jaka87/vetercek_WS/3D prints/WS box/PG gland insert 3.stl

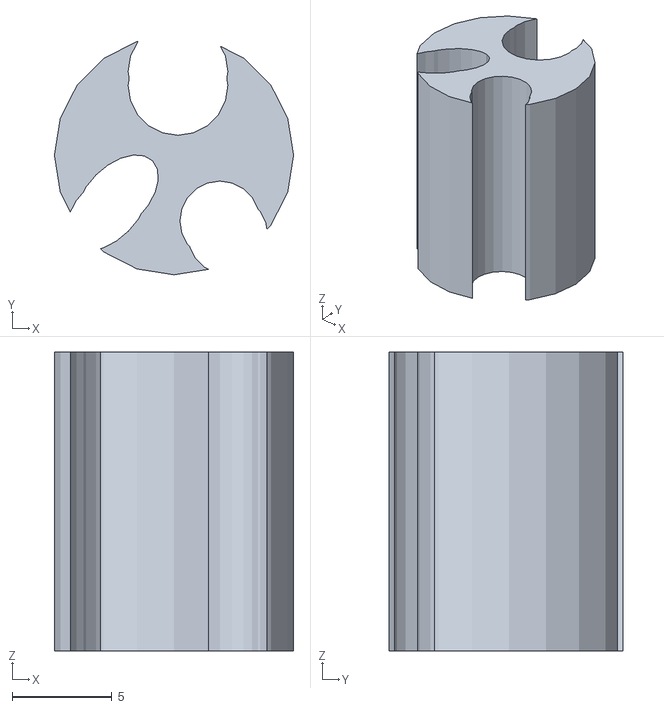
[picture p18: CAD file, 2021-04-03]
3D prints/WS box/PG gland insert 3.stl
12.0 x 11.7 x 15.0
