jaka87/vetercek_WS/3D prints/solar/solar glued.stl

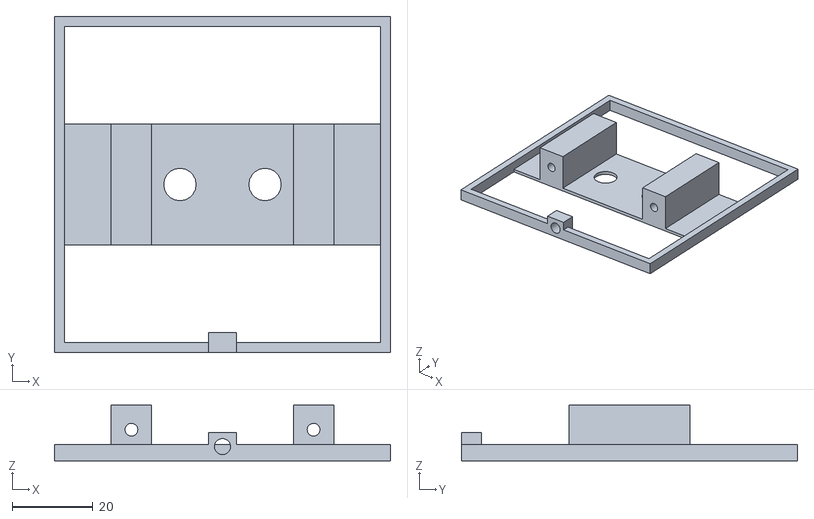
[picture p19: CAD file, 2021-07-03, an earlier design]
3D prints/solar/solar glued.stl
83.0 x 83.0 x 13.7
