jaka87/vetercek_WS/vetercek_SIM7070_modbus/src/BME/Zanshin_BME680.h

// clang-format off
/*! @file Zanshin_BME680.h

@mainpage Arduino Library to access and control a Bosch BME680 Environmental Sensor

@section Zanshin_BME680_section Description

Class definition header for the Bosch BME680 temperature / humidity / pressure / air quality sensor.
The device is described at https://www.bosch-sensortec.com/bst/products/all_products/BME680 and the
datasheet is available from Bosch at
https://ae-bst.resource.bosch.com/media/_tech/media/datasheets/BST-BME680-DS001-00.pdf
\n\n

The BME680 can use either SPI or I2C for communications. This library supports I2C at various bus
speeds as well as SPI using either the standard Arduino hardware SPI or software SPI. Depending upon
the pin configuration a BME680 can have 2 distinct I2C addresses - either 0x76 or 0x77.\n\n

The most recent version of the library is available at https://github.com/SV-Zanshin/BME680 and
extensive documentation of the library as well as descriptions of the various example programs are
described in the project's wiki pages located at https://github.com/SV-Zanshin/BME680/wiki
\n
The BME680 is an extremely small physical package that is so tiny as to be impossible to solder at
home, hence it will be used as part of a third-party breakout board. There are several such boards
available at this time, for example:\n

Company  | Link
-------  | ----------
SparkFun | https://www.sparkfun.com/products/14570
BlueDot  | https://www.bluedot.space/sensor-boards/bme680/
Adafruit |
https://learn.adafruit.com/adafruit-BME680-humidity-barometric-pressure-temperature-sensor-breakout

\n
Bosch supplies sample software that runs on various platforms, including the Arduino family; this
can be downloaded at https://github.com/BoschSensortec/BSEC-Arduino-library. This software is part
of the Bosch "BSEC" (Bosch Sensortec Environmental Cluster) framework and is somewhat bulky and
rather unwieldy for typical Arduino applications, it won't run on most Arduinos and the only example
is for the Arduino Mega 2560 (due to the memory required), hence the decision to make this compact
and rather less abstract library that will run on typical Arduino hardware.

@section license License

This program is free software: you can redistribute it and/or modify it under the terms of the GNU
General Public License as published by the Free Software Foundation, either version 3 of the
License, or (at your option) any later version. This program is distributed in the hope that it will
be useful, but WITHOUT ANY WARRANTY; without even the implied warranty of MERCHANTABILITY or FITNESS
FOR A PARTICULAR PURPOSE.  See the GNU General Public License for more details. You should have
received a copy of the GNU General Public License along with this program.  If not, see
<http://www.gnu.org/licenses/>.

@section author Author

Written by Arnd, https://github.com/SV-Zanshin

@section versions Changelog

Version | Date       | Developer  | Comments
------- | ---------- | ---------- | ---------------------------------------------------------------
1.0.10  | 2020-12-03 | SV-Zanshin | Issue #34 Enhancements from Alain2019 - added measurement functionality
1.0.10  | 2020-12-02 | SV-Zanshin | Issue #33 Optimize library code for size, performance, initializers
1.0.10  | 2020-10-19 | Alain2019  | Issue #32 Change division to bit shifts for clarity
1.0.10  | 2020-10-10 | Alain2019  | Issue #31 Incorrect computation of _H1 and _H2
1.0.9   | 2020-09-27 | SV-Zanshin | Issue #26 added return status for getSensorData
1.0.9   | 2020-09-27 | SV-Zanshin | Issue #26 Corrected computation of gas heater resistance value
1.0.9   | 2020-06-28 | SV-Zanshin | Issue #25 Reformat according to standard c++ style
1.0.8   | 2020-06-20 | SV-Zanshin | Issue #22 added "getI2CAddress()" function
1.0.6   | 2020-05-25 | SV-Zanshin | Issue #17 return value for "setOversampling()"
1.0.6   | 2020-05-25 | SV-Zanshin | Issue #16 I2C "reset()" when using 2 devices
1.0.6   | 2020-05-25 | SV-Zanshin |           General formatting of comments and spell-checking
1.0.6   | 2020-05-24 | SV-Zanshin | Issue #14 Humidity sometimes 100% despite turning on
1.0.6   | 2020-05-24 | SV-Zanshin | Issue #15 Pressure & Temperature oversampling switched
1.0.5   | 2020-05-21 | SV-Zanshin | Issue #12 First call to getSensorData() returns invalid data
1.0.4   | 2020-05-14 | SV-Zanshin | Issue  #9 Allow 2 devices when using I2C
1.0.4   | 2020-05-14 | SV-Zanshin | Issue  #9 Allow 2 devices when using I2C
1.0.3   | 2020-05-09 | SV-Zanshin | Issue  #5 Adjust readings. Subsequently removed code again
1.0.3   | 2020-05-09 | SV-Zanshin | Issue  #8 clean up comments and code
1.0.2   | 2019-01-26 | SV-Zanshin | Issue  #3 Converted documentation to doxygen style
1.0.1   | 2018-07-22 | SV-Zanshin |           Corrected I2C datatypes
1.0.1   | 2018-07-03 | SV-Zanshin | Issue  #1 Added waitForReading and param to getSensorData()
1.0.0   | 2018-07-02 | SV-Zanshin |           Added guard code against multiple I2C constants defs
1.0.0   | 2018-07-01 | SV-Zanshin |           Added and tested I2C, SPI and soft-SPI connections
1.0.0a  | 2018-06-30 | SV-Zanshin |           Cloned from BME280 library and started recoding
*/
// clang-format on
#include <SPI.h>   // Standard SPI library
#include <Wire.h>  // Standard I2C "Wire" library

#include "Arduino.h"  // Arduino data type definitions

#ifndef BME680_h
#define BME680_h  ///< Guard code definition for the header
#define CONCAT_BYTES(msb, lsb) (((uint16_t)msb << 8) | (uint16_t)lsb)  ///< combine msb & lsb bytes
#ifndef _BV
#define _BV(bit) (1 << (bit))  ///< This macro isn't pre-defined on all platforms
#endif
/***************************************************************************************************
** Declare publically visible constants used in the class                                         **
***************************************************************************************************/
#ifndef I2C_MODES                             //   If the I2C_Modes haven't been declared yet
#define I2C_MODES                             ///< Guard code definition for the I2C modes
const uint32_t I2C_STANDARD_MODE{100000};     ///< Default normal I2C 100KHz speed
#endif
const uint32_t SPI_HERZ{500000};  ///< SPI speed in Hz

/***************************************************************************************************
** Declare enumerated types used in the class                                                     **
***************************************************************************************************/
/*! @brief  Enumerate the sensor type */
enum sensorTypes { TemperatureSensor, HumiditySensor, PressureSensor, GasSensor, UnknownSensor };
/*! @brief  Enumerate the Oversampling types */
enum oversamplingTypes {
  SensorOff,
  Oversample16,
  UnknownOversample
};
/*! @brief  Enumerate the iir filter types */
enum iirFilterTypes { IIROff, IIR2, IIR4, IIR8, IIR16, IIR32, IIR64, IIR128, UnknownIIR };

class BME680_Class {
  /*!
   * @class BME680_Class
   * @brief Main BME680 class for the temperature / humidity / pressure sensor
   */
 public:
  BME680_Class();                           // Class constructor (unused)
  ~BME680_Class();                          // Class destructor (unused)
  bool    begin();                          // Start using I2C Communications
  bool    begin(const uint32_t i2cSpeed);   // I2C with a non-default speed
  bool    begin(const uint32_t i2cSpeed, const uint8_t i2cAddress);  // Set speed and I2C Addr.
  uint8_t setOversampling(const uint8_t sensor,  // Set enum sensorType Oversampling
                          const uint8_t sampling = UINT8_MAX) const;  // and return current value
  uint8_t getSensorData(int32_t &temp, int32_t &hum,    // get most recent readings
                        int32_t &press,   //
                        const bool waitSwitch = true);  //
  uint8_t getI2CAddress() const;                        // Return the I2C Address of the BME680
  void    reset();                                      // Reset the BME680
  bool    measuring() const;                            ///< true if currently measuring
  void    triggerMeasurement() const;                   ///< trigger a measurement
 private:                                               //
  bool     commonInitialization();                      ///< Common initialization code
  uint8_t  readByte(const uint8_t addr) const;          ///< Read byte from register address
  uint8_t  readSensors(const bool waitSwitch);          ///< read the registers in one burst
  void     waitForReadings() const;                     ///< Wait for readings to finish
  void     getCalibration();                            ///< Load calibration from registers
  uint8_t  _I2CAddress = 0;                             ///< Default is I2C address is unknown
  uint16_t _I2CSpeed   = 0;                             ///< Default is I2C speed is unknown
  uint8_t  _cs, _sck, _mosi, _miso;                     ///< Hardware and software SPI pins
  uint8_t  _H6, _P10, _res_heat_range;                  ///< unsigned configuration vars
  int8_t   _H3, _H4, _H5, _H7, _G1, _G3, _T3, _P3, _P6, _P7, _res_heat,
      _rng_sw_err;                                            ///< signed configuration vars
  uint16_t _H1, _H2, _T1, _P1;                                ///< unsigned 16bit configuration vars
  int16_t  _G2, _T2, _P2, _P4, _P5, _P8, _P9;                 ///< signed 16bit configuration vars
  int32_t  _tfine, _Temperature, _Pressure, _Humidity;  ///< signed 32bit configuration vars

  /*!
   @section Template functions
   Declare the getData and putData methods as template functions. All device I/O is done through
   these two functions regardless of whether I2C, hardware SPI or software SPI is being used. The
   two functions are designed so that only the address and a variable are passed in and the
   functions determine the size of the parameter variable and reads or writes that many bytes. So
   if a read is called using a character array[10] then 10 bytes are read, if called with a int8
   then only one byte is read. The return value, if used, is the number of bytes read or written.
   Since this is implemented by using template function definitions, they need to be defined in
   this header file rather than in the c++ program library file. The "getData()" function is
   currently not used in the library directly, but the function "readByte()" is used which calls
   the getData().  The "putData()" is called directly in the code.
  */
  template <typename T>
  uint8_t &getData(const uint8_t addr, T &value) const {
    /*!
      @brief     Template for reading from I2C or SPI using any data type
      @details   As a template it can support compile-time data type definitions
      @param[in] addr Memory address
      @param[in] value Data Type "T" to read
      @return    Size of data read in bytes
    */
    uint8_t *      bytePtr    = (uint8_t *)&value;  // Pointer to structure beginning
    static uint8_t structSize = sizeof(T);          // Number of bytes in structure
    if (_I2CAddress)                                // Using I2C if address is non-zero
    {                                               //
      Wire.beginTransmission(_I2CAddress);          // Address the I2C device
      Wire.write(addr);                             // Send register address to read
      Wire.endTransmission();                       // Close transmission
      Wire.requestFrom(_I2CAddress, sizeof(T));     // Request 1 byte of data
      structSize = Wire.available();                // Use the actual number of bytes
      for (uint8_t i = 0; i < structSize; i++)
        *bytePtr++ = Wire.read();  // loop for each byte to be read
    }                              //

    return (structSize);
  }  // of method getData()
  template <typename T>
  uint8_t &putData(const uint8_t addr, const T &value) const {
    /*!
      @brief     Template for writing to I2C or SPI using any data type
      @details   As a template it can support compile-time data type definitions
      @param[in] addr Memory address
      @param[in] value Data Type "T" to write
      @return    Size of data written in bytes
    */
    const uint8_t *bytePtr    = (const uint8_t *)&value;  // Pointer to structure beginning
    static uint8_t structSize = sizeof(T);                // Number of bytes in structure
    if (_I2CAddress)                                      // Using I2C if address is non-zero
    {                                                     //
      Wire.beginTransmission(_I2CAddress);                // Address the I2C device
      Wire.write(addr);                                   // Send register address to write
      for (uint8_t i = 0; i < sizeof(T); i++)
        Wire.write(*bytePtr++);  // loop for each byte to be written
      Wire.endTransmission();    // Close transmission
    } else {
      if (_sck == 0)  // if sck is zero then hardware SPI
      {
        SPI.beginTransaction(
            SPISettings(SPI_HERZ, MSBFIRST, SPI_MODE0));  // start the SPI transaction
        digitalWrite(_cs, LOW);                           // Tell BME680 to listen up
        SPI.transfer(addr & ~0x80);                       // bit 7 is low, so write a byte
        for (uint8_t i = 0; i < structSize; i++) {
          SPI.transfer(*bytePtr++);
        }                         // loop for each byte to be written
        digitalWrite(_cs, HIGH);  // Tell BME680 to stop listening
        SPI.endTransaction();     // End the transaction
      } else                      // Otherwise soft SPI is used
      {
        int8_t  i, j;                     // Loop variables
        uint8_t reply;                    // return byte for soft SPI transfer
        for (i = 0; i < structSize; i++)  // Loop for each byte to read
        {
          reply = 0;                // reset our return byte
          digitalWrite(_cs, LOW);   // Tell BME680 to listen up
          for (j = 7; j >= 0; j--)  // First send the address byte
          {
            digitalWrite(_sck, LOW);                         // set the clock signal
            digitalWrite(_mosi, (addr & ~0x80) & (1 << j));  // set the MOSI pin state
            digitalWrite(_sck, HIGH);                        // reset the clock signal
          }                                                  // of for-next each bit
          for (j = 7; j >= 0; j--)                           // Now read the data at that byte
          {
            reply <<= 1;                               // shift buffer one bit left
            digitalWrite(_sck, LOW);                   // set the clock signal
            digitalWrite(_mosi, *bytePtr & (1 << j));  // set the MOSI pin state
            digitalWrite(_sck, HIGH);                  // reset the clock signal
          }                                            // of for-next each bit
          digitalWrite(_cs, HIGH);                     // Tell BME680 to stop listening
          bytePtr++;                                   // go to next byte to write
        }                                              // of for-next each byte to be read
      }                                                // of  if-then-else we are using hardware SPI//
    }                                                  // of if-then-else we are using I2C
    return (structSize);
  }  // of method putData()
};   // of BME680 class definition
#endif
