jaka87/vetercek_WS/vetercek_SIM7070_modbus/server.py

import socket

UDP_IP_ADDRESS="127.0.0.1"
UDP_PORT_NO=6789

serverSock=socket.socket(socket.AF_INET,socket.SOCK_DGRAM)
serverSock.bind((UDP_IP_ADDRESS,UDP_PORT_NO))


whileTrue:
	data,addr=serverSock.recvfrom(1024)
	dataarray=list(data)
	print(dataarray)
	
	#do stuff with your data thend send response back
	
	messageback=bytearray([1,2,3,4,5])
	serverSock.sendto(messageback, addr)
			
